UC3Music/Shiva/firmware/MIDI_piezo_test/MIDI_piezo_test.ino

/*
  Analog input, analog output, serial output

 Reads an analog input pin, maps the result to a range from 0 to 255
 and uses the result to set the pulsewidth modulation (PWM) of an output pin.
 Also prints the results to the serial monitor.

 The circuit:
 * potentiometer connected to analog pin 0.
   Center pin of the potentiometer goes to the analog pin.
   side pins of the potentiometer go to +5V and ground
 * LED connected from digital pin 9 to ground

 created 29 Dec. 2008
 modified 9 Apr 2012
 by Tom Igoe

 This example code is in the public domain.

 */

// These constants won't change.  They're used to give names
// to the pins used:
const int analogInPin = A0;  // Analog input pin that the potentiometer is attached to
const int analogOutPin = 9; // Analog output pin that the LED is attached to

int sensorValue = 0;        // value read from the pot
int outputValue = 0;        // value output to the PWM (analog out)

const int THRESHOLD = 50;
const int THRESHOLD2 = 50;

// First parameter is the event type (0x09 = note on, 0x08 = note off).
// Second parameter is note-on/note-off, combined with the channel.
// Channel can be anything between 0-15. Typically reported to the user as 1-16.
// Third parameter is the note number (48 = middle C).
// Fourth parameter is the velocity (64 = normal, 127 = fastest).

void noteOn(byte channel, byte pitch, byte velocity) {
  MIDIEvent noteOn = {0x09, 0x90 | channel, pitch, velocity};
  MIDIUSB.write(noteOn);
}

void noteOff(byte channel, byte pitch, byte velocity) {
  MIDIEvent noteOff = {0x08, 0x80 | channel, pitch, velocity};
  MIDIUSB.write(noteOff);
}

// First parameter is the event type (0x0B = control change).
// Second parameter is the event type, combined with the channel.
// Third parameter is the control number number (0-119).
// Fourth parameter is the control value (0-127).

void controlChange(byte channel, byte control, byte value) {
  MIDIEvent event = {0x0B, 0xB0 | channel, control, value};
  MIDIUSB.write(event);
}


void setup() {
  // initialize serial communications at 9600 bps:
  Serial.begin(9600);
}

void loop() {
  static uint8_t state = 0;
  
  // read the analog in value:
  sensorValue = analogRead(analogInPin);

  if (state == 0) {
    if (sensorValue > THRESHOLD) {
      // print the results to the serial monitor:
      Serial.print("sensor = " );
      Serial.println(sensorValue);  

      state = 1;

      // midi note
      noteOn(9, 49, 64);   // Channel 0, middle C, normal velocity
      MIDIUSB.flush();
    }
  }
  else if (state == 1) {
    if (sensorValue < THRESHOLD2) {
      state = 0;

      // note off
      noteOff(9, 49, 64);  // Channel 0, middle C, normal velocity
      MIDIUSB.flush();
    }
  }
  



  // wait 2 milliseconds before the next loop
  // for the analog-to-digital converter to settle
  // after the last reading:
  delay(2);
}
